ninomegadriver/TDBABootleg/ESP32_HW_Fantastic/resources/menu_kong.png

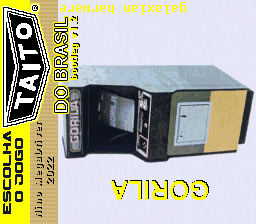
ESP32_HW_Fantastic/resources/menu_kong.png
