ninomegadriver/TDBABootleg/ESP32_HW_Invaders/resources/bkp/menu_indian.png

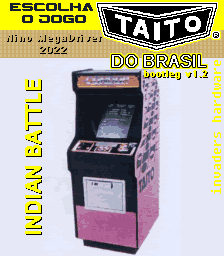
ESP32_HW_Invaders/resources/bkp/menu_indian.png
