ninomegadriver/TDBABootleg/ESP32_HW_Invaders/resources/bkp/menu_invaders.png

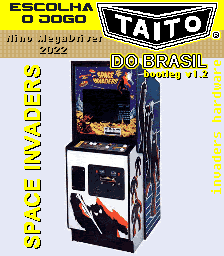
ESP32_HW_Invaders/resources/bkp/menu_invaders.png
