ninomegadriver/TDBABootleg/ESP32_HW_Invaders/resources/menu_galactica.png

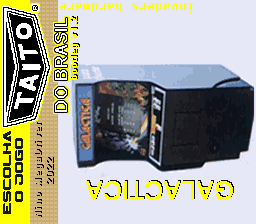
ESP32_HW_Invaders/resources/menu_galactica.png
