ninomegadriver/TDBABootleg/ESP32_HW_Invaders/resources/menu_indian.png

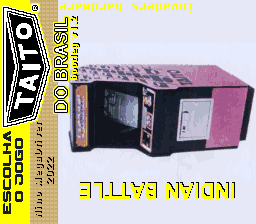
ESP32_HW_Invaders/resources/menu_indian.png
