ninomegadriver/TDBABootleg/ESP32_HW_Invaders/resources/menu_invaders.png

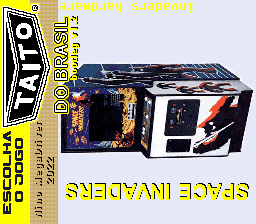
ESP32_HW_Invaders/resources/menu_invaders.png
