ninomegadriver/TDBABootleg/ESP32_HW_Fantastic/munch.hpp

#pragma GCC optimize ("O3")

// MAME: pacmanbl

void munch_pal(){
   pixel[0] = DisplayController.createRawPixel(RGB888(0,0,0));
   pixel[1] = DisplayController.createRawPixel(RGB888(0,0,0));
   pixel[2] = DisplayController.createRawPixel(RGB888(0,0,0));
   pixel[3] = DisplayController.createRawPixel(RGB888(195,195,217));
   pixel[4] = DisplayController.createRawPixel(RGB888(0,0,0));
   pixel[5] = DisplayController.createRawPixel(RGB888(195,62,0));
   pixel[6] = DisplayController.createRawPixel(RGB888(0,0,217));
   pixel[7] = DisplayController.createRawPixel(RGB888(224,224,0));
   pixel[8] = DisplayController.createRawPixel(RGB888(0,0,0));
   pixel[9] = DisplayController.createRawPixel(RGB888(0,91,217));
   pixel[10] = DisplayController.createRawPixel(RGB888(224,0,0));
   pixel[11] = DisplayController.createRawPixel(RGB888(224,224,0));
   pixel[12] = DisplayController.createRawPixel(RGB888(0,0,0));
   pixel[13] = DisplayController.createRawPixel(RGB888(0,0,217));
   pixel[14] = DisplayController.createRawPixel(RGB888(133,0,217));
   pixel[15] = DisplayController.createRawPixel(RGB888(224,0,0));
   pixel[16] = DisplayController.createRawPixel(RGB888(0,0,0));
   pixel[17] = DisplayController.createRawPixel(RGB888(0,0,217));
   pixel[18] = DisplayController.createRawPixel(RGB888(0,133,148));
   pixel[19] = DisplayController.createRawPixel(RGB888(133,29,0));
   pixel[20] = DisplayController.createRawPixel(RGB888(0,0,0));
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
1,1,0,0,0,0,0,1,1,0,0,0,0,0,0,0,0,0,0,0,0,0,0,0,0,0,0,0,0,0,0,0,0,
0,0,0,0,0,0,0,0,0,0,0,0,0,0,1,1,0,0,0,0,0,1,1,1,1,0,0,0,0,1,1,1,1,
0,0,0,0,0,1,1,0,0,0,0,0,0,0,0,0,0,0,0,0,0,0,0,0,0,0,0,0,1,1,1,1,0,
0,0,1,1,1,1,1,1,0,1,1,1,1,1,1,1,1,1,1,1,1,1,1,1,1,1,1,1,1,1,1,1,1,
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
