ninomegadriver/TDBABootleg/ESP32_HW_Invaders/galactic.hpp

#pragma GCC optimize ("O3")

#include "Arduino.h"

void galactic_layout(){
  for( int i=0; i<260; i++ ) {
    int   c = 2;                // verde
    if(i>=187 && i<=210) c = 3; // vermelho
    if(i>=60 && i<=186)  c = 4; // amarelo
    if(i>=45 && i<=59)   c = 5; // azul
    scanLineColor[i] = c;
  }
}

const uint8_t galactic[] = {
    0x00, 0x00, 0x00, 0xC3, 0x9B, 0x00, 0xFF, 0xFF, 0xC3, 0x40, 0x00, 0xFF, 0xFF, 0xFF, 0xFF, 0xFF, 0xC3, 0x40, 0x00, 0xFF, 
    0xFF, 0xFF, 0xFF, 0xFF, 0xC3, 0x40, 0x00, 0xFF, 0xFF, 0xFF, 0xFF, 0xFF, 0x77, 0x23, 0x05, 0xC2, 0x20, 0x00, 0xC9, 0xFF, 
    0x87, 0xE1, 0x5F, 0x16, 0x00, 0x19, 0x5E, 0x23, 0x56, 0xEB, 0xE9, 0xFF, 0xFF, 0xFF, 0xFF, 0xFF, 0x85, 0x6F, 0x3E, 0x00, 
    0x8C, 0x67, 0x7E, 0xC9, 0xF5, 0xC5, 0xD5, 0xE5, 0xD3, 0x06, 0x3A, 0x15, 0x20, 0x32, 0x16, 0x20, 0x3A, 0x13, 0x20, 0x32, 
    0x15, 0x20, 0x2A, 0x10, 0x20, 0x22, 0x13, 0x20, 0xDB, 0x00, 0x32, 0x12, 0x20, 0xDB, 0x02, 0x32, 0x11, 0x20, 0xDB, 0x01, 
    0x32, 0x10, 0x20, 0x21, 0x5F, 0x22, 0x35, 0xCD, 0x1F, 0x4E, 0xCD, 0x34, 0x4E, 0xCD, 0x35, 0x50, 0xCD, 0x96, 0x52, 0x3A, 
    0x3E, 0x20, 0xD3, 0x03, 0x3A, 0x3F, 0x20, 0xD3, 0x05, 0xCD, 0xD5, 0x1D, 0x21, 0x96, 0x00, 0xE5, 0x3A, 0x05, 0x20, 0xEF, 
    0xEB, 0x04, 0x2E, 0x05, 0x6B, 0x07, 0xAB, 0x08, 0x1F, 0x0B, 0xE1, 0xD1, 0xC1, 0xF1, 0xC9, 0x31, 0x00, 0x24, 0x3E, 0x00, 
    0xD3, 0x03, 0x32, 0x3E, 0x20, 0x3E, 0x0F, 0xD3, 0x05, 0x32, 0x3F, 0x20, 0x3E, 0xFF, 0xD3, 0x07, 0x21, 0x00, 0x20, 0xAF, 
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
    0x24, 0x1C, 0x1D, 0x0A, 0x1B, 0x1D, 0x24, 0x24, 0xFF, 0x0B, 0x2D, 0x13, 0x18, 0x10, 0x0A, 0x0D, 0x18, 0x1B, 0x24, 0x00, 
    0x01, 0xFF, 0x0B, 0x2D, 0x13, 0x18, 0x10, 0x0A, 0x0D, 0x18, 0x1B, 0x24, 0x00, 0x02, 0xFF, 0x1F, 0x2E, 0x1B, 0x0E, 0x0C, 
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
};
