ninomegadriver/TDBABootleg/ESP32_HW_Invaders/i8080.c

#pragma GCC optimize ("O3")


#include "i8080.h"

// this array defines the number of cycles one opcode takes.
// note that there are some special cases: conditional RETs and CALLs
// add +6 cycles if the condition is met
// clang-format off
static const uint8_t OPCODES_CYCLES[256] = {
//  0  1   2   3   4   5   6   7   8  9   A   B   C   D   E  F
    4, 10, 7,  5,  5,  5,  7,  4,  4, 10, 7,  5,  5,  5,  7, 4,  // 0
    4, 10, 7,  5,  5,  5,  7,  4,  4, 10, 7,  5,  5,  5,  7, 4,  // 1
    4, 10, 16, 5,  5,  5,  7,  4,  4, 10, 16, 5,  5,  5,  7, 4,  // 2
    4, 10, 13, 5,  10, 10, 10, 4,  4, 10, 13, 5,  5,  5,  7, 4,  // 3
    5, 5,  5,  5,  5,  5,  7,  5,  5, 5,  5,  5,  5,  5,  7, 5,  // 4
    5, 5,  5,  5,  5,  5,  7,  5,  5, 5,  5,  5,  5,  5,  7, 5,  // 5
    5, 5,  5,  5,  5,  5,  7,  5,  5, 5,  5,  5,  5,  5,  7, 5,  // 6
    7, 7,  7,  7,  7,  7,  7,  7,  5, 5,  5,  5,  5,  5,  7, 5,  // 7
    4, 4,  4,  4,  4,  4,  7,  4,  4, 4,  4,  4,  4,  4,  7, 4,  // 8
    4, 4,  4,  4,  4,  4,  7,  4,  4, 4,  4,  4,  4,  4,  7, 4,  // 9
    4, 4,  4,  4,  4,  4,  7,  4,  4, 4,  4,  4,  4,  4,  7, 4,  // A
    4, 4,  4,  4,  4,  4,  7,  4,  4, 4,  4,  4,  4,  4,  7, 4,  // B
    5, 10, 10, 10, 11, 11, 7,  11, 5, 10, 10, 10, 11, 17, 7, 11, // C
    5, 10, 10, 10, 11, 11, 7,  11, 5, 10, 10, 10, 11, 17, 7, 11, // D
    5, 10, 10, 18, 11, 11, 7,  11, 5, 5,  10, 4,  11, 17, 7, 11, // E
    5, 10, 10, 4,  11, 11, 7,  11, 5, 5,  10, 4,  11, 17, 7, 11  // F
};
// clang-format on

static const char* DISASSEMBLE_TABLE[] = {"nop", "lxi b,#", "stax b", "inx b",
    "inr b", "dcr b", "mvi b,#", "rlc", "ill", "dad b", "ldax b", "dcx b",
    "inr c", "dcr c", "mvi c,#", "rrc", "ill", "lxi d,#", "stax d", "inx d",
    "inr d", "dcr d", "mvi d,#", "ral", "ill", "dad d", "ldax d", "dcx d",
    "inr e", "dcr e", "mvi e,#", "rar", "ill", "lxi h,#", "shld", "inx h",
    "inr h", "dcr h", "mvi h,#", "daa", "ill", "dad h", "lhld", "dcx h",
    "inr l", "dcr l", "mvi l,#", "cma", "ill", "lxi sp,#", "sta $", "inx sp",
    "inr M", "dcr M", "mvi M,#", "stc", "ill", "dad sp", "lda $", "dcx sp",
    "inr a", "dcr a", "mvi a,#", "cmc", "mov b,b", "mov b,c", "mov b,d",
    "mov b,e", "mov b,h", "mov b,l", "mov b,M", "mov b,a", "mov c,b", "mov c,c",
    "mov c,d", "mov c,e", "mov c,h", "mov c,l", "mov c,M", "mov c,a", "mov d,b",
    "mov d,c", "mov d,d", "mov d,e", "mov d,h", "mov d,l", "mov d,M", "mov d,a",
    "mov e,b", "mov e,c", "mov e,d", "mov e,e", "mov e,h", "mov e,l", "mov e,M",
    "mov e,a", "mov h,b", "mov h,c", "mov h,d", "mov h,e", "mov h,h", "mov h,l",
    "mov h,M", "mov h,a", "mov l,b", "mov l,c", "mov l,d", "mov l,e", "mov l,h",
    "mov l,l", "mov l,M", "mov l,a", "mov M,b", "mov M,c", "mov M,d", "mov M,e",
    "mov M,h", "mov M,l", "hlt", "mov M,a", "mov a,b", "mov a,c", "mov a,d",
    "mov a,e", "mov a,h", "mov a,l", "mov a,M", "mov a,a", "add b", "add c",
    "add d", "add e", "add h", "add l", "add M", "add a", "adc b", "adc c",
    "adc d", "adc e", "adc h", "adc l", "adc M", "adc a", "sub b", "sub c",
    "sub d", "sub e", "sub h", "sub l", "sub M", "sub a", "sbb b", "sbb c",
    "sbb d", "sbb e", "sbb h", "sbb l", "sbb M", "sbb a", "ana b", "ana c",
    "ana d", "ana e", "ana h", "ana l", "ana M", "ana a", "xra b", "xra c",
    "xra d", "xra e", "xra h", "xra l", "xra M", "xra a", "ora b", "ora c",
    "ora d", "ora e", "ora h", "ora l", "ora M", "ora a", "cmp b", "cmp c",
    "cmp d", "cmp e", "cmp h", "cmp l", "cmp M", "cmp a", "rnz", "pop b",
    "jnz $", "jmp $", "cnz $", "push b", "adi #", "rst 0", "rz", "ret", "jz $",
    "ill", "cz $", "call $", "aci #", "rst 1", "rnc", "pop d", "jnc $", "out p",
    "cnc $", "push d", "sui #", "rst 2", "rc", "ill", "jc $", "in p", "cc $",
    "ill", "sbi #", "rst 3", "rpo", "pop h", "jpo $", "xthl", "cpo $", "push h",
    "ani #", "rst 4", "rpe", "pchl", "jpe $", "xchg", "cpe $", "ill", "xri #",
    "rst 5", "rp", "pop psw", "jp $", "di", "cp $", "push psw", "ori #",
    "rst 6", "rm", "sphl", "jm $", "ei", "cm $", "ill", "cpi #", "rst 7"};

#define SET_ZSP(c, val) \
  do { \
    c->zf = (val) == 0; \
    c->sf = (val) >> 7; \
    c->pf = parity(val); \
  } while (0)

// memory helpers (the only four to use `read_byte` and `write_byte` function
// pointers)

// reads a byte from memory
static inline uint8_t i8080_rb(i8080* const c, uint16_t addr) {
  return c->read_byte(c->userdata, addr);
}

// writes a byte to memory
static inline void i8080_wb(i8080* const c, uint16_t addr, uint8_t val) {
  c->write_byte(c->userdata, addr, val);
}

// reads a word from memory
static inline uint16_t i8080_rw(i8080* const c, uint16_t addr) {
  return c->read_byte(c->userdata, addr + 1) << 8 |
         c->read_byte(c->userdata, addr);
}

// writes a word to memory
static inline void i8080_ww(i8080* const c, uint16_t addr, uint16_t val) {
  c->write_byte(c->userdata, addr, val & 0xFF);
  c->write_byte(c->userdata, addr + 1, val >> 8);
}

// returns the next byte in memory (and updates the program counter)
static inline uint8_t i8080_next_byte(i8080* const c) {
  return i8080_rb(c, c->pc++);
}

// returns the next word in memory (and updates the program counter)
static inline uint16_t i8080_next_word(i8080* const c) {
  uint16_t result = i8080_rw(c, c->pc);
  c->pc += 2;
  return result;
}

// paired registers helpers (setters and getters)
static inline void i8080_set_bc(i8080* const c, uint16_t val) {
  c->b = val >> 8;
  c->c = val & 0xFF;
}

static inline void i8080_set_de(i8080* const c, uint16_t val) {
  c->d = val >> 8;
  c->e = val & 0xFF;
}

static inline void i8080_set_hl(i8080* const c, uint16_t val) {
  c->h = val >> 8;
  c->l = val & 0xFF;
}

static inline uint16_t i8080_get_bc(i8080* const c) {
  return (c->b << 8) | c->c;
}

static inline uint16_t i8080_get_de(i8080* const c) {
  return (c->d << 8) | c->e;
}

static inline uint16_t i8080_get_hl(i8080* const c) {
  return (c->h << 8) | c->l;
}

// stack helpers

// pushes a value into the stack and updates the stack pointer
static inline void i8080_push_stack(i8080* const c, uint16_t val) {
  c->sp -= 2;
  i8080_ww(c, c->sp, val);
}

// pops a value from the stack and updates the stack pointer
static inline uint16_t i8080_pop_stack(i8080* const c) {
  uint16_t val = i8080_rw(c, c->sp);
  c->sp += 2;
  return val;
}

// opcodes

// returns the parity of byte: 0 if number of 1 bits in `val` is odd, else 1
static inline bool parity(uint8_t val) {
  uint8_t nb_one_bits = 0;
  for (int i = 0; i < 8; i++) {
    nb_one_bits += ((val >> i) & 1);
  }

  return (nb_one_bits & 1) == 0;
}

// returns if there was a carry between bit "bit_no" and "bit_no - 1" when
// executing "a + b + cy"
static inline bool carry(int bit_no, uint8_t a, uint8_t b, bool cy) {
  int16_t result = a + b + cy;
  int16_t carry = result ^ a ^ b;
  return carry & (1 << bit_no);
}

// adds a value (+ an optional carry flag) to a register
static inline void i8080_add(
    i8080* const c, uint8_t* const reg, uint8_t val, bool cy) {
  uint8_t result = *reg + val + cy;
  c->cf = carry(8, *reg, val, cy);
  c->hf = carry(4, *reg, val, cy);
  SET_ZSP(c, result);
  *reg = result;
}

// substracts a byte (+ an optional carry flag) from a register
// see https://stackoverflow.com/a/8037485
static inline void i8080_sub(
    i8080* const c, uint8_t* const reg, uint8_t val, bool cy) {
  i8080_add(c, reg, ~val, !cy);
  c->cf = !c->cf;
}

// adds a word to HL
static inline void i8080_dad(i8080* const c, uint16_t val) {
  c->cf = ((i8080_get_hl(c) + val) >> 16) & 1;
  i8080_set_hl(c, i8080_get_hl(c) + val);
}

// increments a byte
static inline uint8_t i8080_inr(i8080* const c, uint8_t val) {
  uint8_t result = val + 1;
  c->hf = (result & 0xF) == 0;
  SET_ZSP(c, result);
  return result;
}

// decrements a byte
static inline uint8_t i8080_dcr(i8080* const c, uint8_t val) {
  uint8_t result = val - 1;
  c->hf = !((result & 0xF) == 0xF);
  SET_ZSP(c, result);
  return result;
}

// executes a logic "and" between register A and a byte, then stores the
// result in register A
static inline void i8080_ana(i8080* const c, uint8_t val) {
  uint8_t result = c->a & val;
  c->cf = 0;
  c->hf = ((c->a | val) & 0x08) != 0;
  SET_ZSP(c, result);
  c->a = result;
}

// executes a logic "xor" between register A and a byte, then stores the
// result in register A
static inline void i8080_xra(i8080* const c, uint8_t val) {
  c->a ^= val;
  c->cf = 0;
  c->hf = 0;
  SET_ZSP(c, c->a);
}

// executes a logic "or" between register A and a byte, then stores the
// result in register A
static inline void i8080_ora(i8080* const c, uint8_t val) {
  c->a |= val;
  c->cf = 0;
  c->hf = 0;
  SET_ZSP(c, c->a);
}

// compares the register A to another byte
static inline void i8080_cmp(i8080* const c, uint8_t val) {
  int16_t result = c->a - val;
  c->cf = result >> 8;
  c->hf = ~(c->a ^ result ^ val) & 0x10;
  SET_ZSP(c, result & 0xFF);
}

// sets the program counter to a given address
static inline void i8080_jmp(i8080* const c, uint16_t addr) {
  c->pc = addr;
}

// jumps to next address pointed by the next word in memory if a condition
// is met
static inline void i8080_cond_jmp(i8080* const c, bool condition) {
  uint16_t addr = i8080_next_word(c);
  if (condition) {
    c->pc = addr;
  }
}

// pushes the current pc to the stack, then jumps to an address
static inline void i8080_call(i8080* const c, uint16_t addr) {
  i8080_push_stack(c, c->pc);
  i8080_jmp(c, addr);
}

// calls to next word in memory if a condition is met
static inline void i8080_cond_call(i8080* const c, bool condition) {
  uint16_t addr = i8080_next_word(c);
  if (condition) {
    i8080_call(c, addr);
    c->cyc += 6;
  }
}

// returns from subroutine
static inline void i8080_ret(i8080* const c) {
  c->pc = i8080_pop_stack(c);
}

// returns from subroutine if a condition is met
static inline void i8080_cond_ret(i8080* const c, bool condition) {
  if (condition) {
    i8080_ret(c);
    c->cyc += 6;
  }
}

// pushes register A and the flags into the stack
static inline void i8080_push_psw(i8080* const c) {
  // note: bit 3 and 5 are always 0
  uint8_t psw = 0;
  psw |= c->sf << 7;
  psw |= c->zf << 6;
  psw |= c->hf << 4;
  psw |= c->pf << 2;
  psw |= 1 << 1; // bit 1 is always 1
  psw |= c->cf << 0;
  i8080_push_stack(c, c->a << 8 | psw);
}

// pops register A and the flags from the stack
static inline void i8080_pop_psw(i8080* const c) {
  uint16_t af = i8080_pop_stack(c);
  c->a = af >> 8;
  uint8_t psw = af & 0xFF;

  c->sf = (psw >> 7) & 1;
  c->zf = (psw >> 6) & 1;
  c->hf = (psw >> 4) & 1;
  c->pf = (psw >> 2) & 1;
  c->cf = (psw >> 0) & 1;
}

// rotate register A left
static inline void i8080_rlc(i8080* const c) {
  c->cf = c->a >> 7;
  c->a = (c->a << 1) | c->cf;
}

// rotate register A right
static inline void i8080_rrc(i8080* const c) {
  c->cf = c->a & 1;
  c->a = (c->a >> 1) | (c->cf << 7);
}

// rotate register A left with the carry flag
static inline void i8080_ral(i8080* const c) {
  bool cy = c->cf;
  c->cf = c->a >> 7;
  c->a = (c->a << 1) | cy;
}

// rotate register A right with the carry flag
static inline void i8080_rar(i8080* const c) {
  bool cy = c->cf;
  c->cf = c->a & 1;
  c->a = (c->a >> 1) | (cy << 7);
}

// Decimal Adjust Accumulator: the eight-bit number in register A is adjusted
// to form two four-bit binary-coded-decimal digits.
// For example, if A=$2B and DAA is executed, A becomes $31.
static inline void i8080_daa(i8080* const c) {
  bool cy = c->cf;
  uint8_t correction = 0;

  uint8_t lsb = c->a & 0x0F;
  uint8_t msb = c->a >> 4;

  if (c->hf || lsb > 9) {
    correction += 0x06;
  }

  if (c->cf || msb > 9 || (msb >= 9 && lsb > 9)) {
    correction += 0x60;
    cy = 1;
  }

  i8080_add(c, &c->a, correction, 0);
  c->cf = cy;
}

// switches the value of registers DE and HL
static inline void i8080_xchg(i8080* const c) {
  uint16_t de = i8080_get_de(c);
  i8080_set_de(c, i8080_get_hl(c));
  i8080_set_hl(c, de);
}

// switches the value of a word at (sp) and HL
static inline void i8080_xthl(i8080* const c) {
  uint16_t val = i8080_rw(c, c->sp);
  i8080_ww(c, c->sp, i8080_get_hl(c));
  i8080_set_hl(c, val);
}

// executes one opcode
static inline void i8080_execute(i8080* const c, uint8_t opcode) {
  c->cyc += OPCODES_CYCLES[opcode];

  // when DI is executed, interrupts won't be serviced
  // until the end of next instruction:
  if (c->interrupt_delay > 0) {
    c->interrupt_delay -= 1;
  }

  switch (opcode) {
  case 0x7F: c->a = c->a; break; // MOV A,A
  case 0x78: c->a = c->b; break; // MOV A,B
  case 0x79: c->a = c->c; break; // MOV A,C
  case 0x7A: c->a = c->d; break; // MOV A,D
  case 0x7B: c->a = c->e; break; // MOV A,E
  case 0x7C: c->a = c->h; break; // MOV A,H
  case 0x7D: c->a = c->l; break; // MOV A,L
  case 0x7E: c->a = i8080_rb(c, i8080_get_hl(c)); break; // MOV A,M

  case 0x0A: c->a = i8080_rb(c, i8080_get_bc(c)); break; // LDAX B
  case 0x1A: c->a = i8080_rb(c, i8080_get_de(c)); break; // LDAX D
  case 0x3A: c->a = i8080_rb(c, i8080_next_word(c)); break; // LDA word

  case 0x47: c->b = c->a; break; // MOV B,A
  case 0x40: c->b = c->b; break; // MOV B,B
  case 0x41: c->b = c->c; break; // MOV B,C
  case 0x42: c->b = c->d; break; // MOV B,D
  case 0x43: c->b = c->e; break; // MOV B,E
  case 0x44: c->b = c->h; break; // MOV B,H
  case 0x45: c->b = c->l; break; // MOV B,L
  case 0x46: c->b = i8080_rb(c, i8080_get_hl(c)); break; // MOV B,M

  case 0x4F: c->c = c->a; break; // MOV C,A
  case 0x48: c->c = c->b; break; // MOV C,B
  case 0x49: c->c = c->c; break; // MOV C,C
  case 0x4A: c->c = c->d; break; // MOV C,D
  case 0x4B: c->c = c->e; break; // MOV C,E
  case 0x4C: c->c = c->h; break; // MOV C,H
  case 0x4D: c->c = c->l; break; // MOV C,L
  case 0x4E: c->c = i8080_rb(c, i8080_get_hl(c)); break; // MOV C,M

  case 0x57: c->d = c->a; break; // MOV D,A
  case 0x50: c->d = c->b; break; // MOV D,B
  case 0x51: c->d = c->c; break; // MOV D,C
  case 0x52: c->d = c->d; break; // MOV D,D
  case 0x53: c->d = c->e; break; // MOV D,E
  case 0x54: c->d = c->h; break; // MOV D,H
  case 0x55: c->d = c->l; break; // MOV D,L
  case 0x56: c->d = i8080_rb(c, i8080_get_hl(c)); break; // MOV D,M

  case 0x5F: c->e = c->a; break; // MOV E,A
  case 0x58: c->e = c->b; break; // MOV E,B
  case 0x59: c->e = c->c; break; // MOV E,C
  case 0x5A: c->e = c->d; break; // MOV E,D
  case 0x5B: c->e = c->e; break; // MOV E,E
  case 0x5C: c->e = c->h; break; // MOV E,H
  case 0x5D: c->e = c->l; break; // MOV E,L
  case 0x5E: c->e = i8080_rb(c, i8080_get_hl(c)); break; // MOV E,M

  case 0x67: c->h = c->a; break; // MOV H,A
  case 0x60: c->h = c->b; break; // MOV H,B
  case 0x61: c->h = c->c; break; // MOV H,C
  case 0x62: c->h = c->d; break; // MOV H,D
  case 0x63: c->h = c->e; break; // MOV H,E
  case 0x64: c->h = c->h; break; // MOV H,H
  case 0x65: c->h = c->l; break; // MOV H,L
  case 0x66: c->h = i8080_rb(c, i8080_get_hl(c)); break; // MOV H,M

  case 0x6F: c->l = c->a; break; // MOV L,A
  case 0x68: c->l = c->b; break; // MOV L,B
  case 0x69: c->l = c->c; break; // MOV L,C
  case 0x6A: c->l = c->d; break; // MOV L,D
  case 0x6B: c->l = c->e; break; // MOV L,E
  case 0x6C: c->l = c->h; break; // MOV L,H
  case 0x6D: c->l = c->l; break; // MOV L,L
  case 0x6E: c->l = i8080_rb(c, i8080_get_hl(c)); break; // MOV L,M

  case 0x77: i8080_wb(c, i8080_get_hl(c), c->a); break; // MOV M,A
  case 0x70: i8080_wb(c, i8080_get_hl(c), c->b); break; // MOV M,B
  case 0x71: i8080_wb(c, i8080_get_hl(c), c->c); break; // MOV M,C
  case 0x72: i8080_wb(c, i8080_get_hl(c), c->d); break; // MOV M,D
  case 0x73: i8080_wb(c, i8080_get_hl(c), c->e); break; // MOV M,E
  case 0x74: i8080_wb(c, i8080_get_hl(c), c->h); break; // MOV M,H
  case 0x75: i8080_wb(c, i8080_get_hl(c), c->l); break; // MOV M,L

  case 0x3E: c->a = i8080_next_byte(c); break; // MVI A,byte
  case 0x06: c->b = i8080_next_byte(c); break; // MVI B,byte
  case 0x0E: c->c = i8080_next_byte(c); break; // MVI C,byte
  case 0x16: c->d = i8080_next_byte(c); break; // MVI D,byte
  case 0x1E: c->e = i8080_next_byte(c); break; // MVI E,byte
  case 0x26: c->h = i8080_next_byte(c); break; // MVI H,byte
  case 0x2E: c->l = i8080_next_byte(c); break; // MVI L,byte
  case 0x36:
    i8080_wb(c, i8080_get_hl(c), i8080_next_byte(c));
    break; // MVI M,byte

  case 0x02: i8080_wb(c, i8080_get_bc(c), c->a); break; // STAX B
  case 0x12: i8080_wb(c, i8080_get_de(c), c->a); break; // STAX D
  case 0x32: i8080_wb(c, i8080_next_word(c), c->a); break; // STA word

  case 0x01: i8080_set_bc(c, i8080_next_word(c)); break; // LXI B,word
  case 0x11: i8080_set_de(c, i8080_next_word(c)); break; // LXI D,word
  case 0x21: i8080_set_hl(c, i8080_next_word(c)); break; // LXI H,word
  case 0x31: c->sp = i8080_next_word(c); break; // LXI SP,word
  case 0x2A: i8080_set_hl(c, i8080_rw(c, i8080_next_word(c))); break; // LHLD
  case 0x22: i8080_ww(c, i8080_next_word(c), i8080_get_hl(c)); break; // SHLD
  case 0xF9: c->sp = i8080_get_hl(c); break; // SPHL

  case 0xEB: i8080_xchg(c); break; // XCHG
  case 0xE3: i8080_xthl(c); break; // XTHL

  case 0x87: i8080_add(c, &c->a, c->a, 0); break; // ADD A
  case 0x80: i8080_add(c, &c->a, c->b, 0); break; // ADD B
  case 0x81: i8080_add(c, &c->a, c->c, 0); break; // ADD C
  case 0x82: i8080_add(c, &c->a, c->d, 0); break; // ADD D
  case 0x83: i8080_add(c, &c->a, c->e, 0); break; // ADD E
  case 0x84: i8080_add(c, &c->a, c->h, 0); break; // ADD H
  case 0x85: i8080_add(c, &c->a, c->l, 0); break; // ADD L
  case 0x86:
    i8080_add(c, &c->a, i8080_rb(c, i8080_get_hl(c)), 0);
    break; // ADD M
  case 0xC6: i8080_add(c, &c->a, i8080_next_byte(c), 0); break; // ADI byte

  case 0x8F: i8080_add(c, &c->a, c->a, c->cf); break; // ADC A
  case 0x88: i8080_add(c, &c->a, c->b, c->cf); break; // ADC B
  case 0x89: i8080_add(c, &c->a, c->c, c->cf); break; // ADC C
  case 0x8A: i8080_add(c, &c->a, c->d, c->cf); break; // ADC D
  case 0x8B: i8080_add(c, &c->a, c->e, c->cf); break; // ADC E
  case 0x8C: i8080_add(c, &c->a, c->h, c->cf); break; // ADC H
  case 0x8D: i8080_add(c, &c->a, c->l, c->cf); break; // ADC L
  case 0x8E:
    i8080_add(c, &c->a, i8080_rb(c, i8080_get_hl(c)), c->cf);
    break; // ADC M
  case 0xCE: i8080_add(c, &c->a, i8080_next_byte(c), c->cf); break; // ACI byte

  case 0x97: i8080_sub(c, &c->a, c->a, 0); break; // SUB A
  case 0x90: i8080_sub(c, &c->a, c->b, 0); break; // SUB B
  case 0x91: i8080_sub(c, &c->a, c->c, 0); break; // SUB C
  case 0x92: i8080_sub(c, &c->a, c->d, 0); break; // SUB D
  case 0x93: i8080_sub(c, &c->a, c->e, 0); break; // SUB E
  case 0x94: i8080_sub(c, &c->a, c->h, 0); break; // SUB H
  case 0x95: i8080_sub(c, &c->a, c->l, 0); break; // SUB L
  case 0x96:
    i8080_sub(c, &c->a, i8080_rb(c, i8080_get_hl(c)), 0);
    break; // SUB M
  case 0xD6: i8080_sub(c, &c->a, i8080_next_byte(c), 0); break; // SUI byte

  case 0x9F: i8080_sub(c, &c->a, c->a, c->cf); break; // SBB A
  case 0x98: i8080_sub(c, &c->a, c->b, c->cf); break; // SBB B
  case 0x99: i8080_sub(c, &c->a, c->c, c->cf); break; // SBB C
  case 0x9A: i8080_sub(c, &c->a, c->d, c->cf); break; // SBB D
  case 0x9B: i8080_sub(c, &c->a, c->e, c->cf); break; // SBB E
  case 0x9C: i8080_sub(c, &c->a, c->h, c->cf); break; // SBB H
  case 0x9D: i8080_sub(c, &c->a, c->l, c->cf); break; // SBB L
  case 0x9E:
    i8080_sub(c, &c->a, i8080_rb(c, i8080_get_hl(c)), c->cf);
    break; // SBB M
  case 0xDE: i8080_sub(c, &c->a, i8080_next_byte(c), c->cf); break; // SBI byte

  case 0x09: i8080_dad(c, i8080_get_bc(c)); break; // DAD B
  case 0x19: i8080_dad(c, i8080_get_de(c)); break; // DAD D
  case 0x29: i8080_dad(c, i8080_get_hl(c)); break; // DAD H
  case 0x39: i8080_dad(c, c->sp); break; // DAD SP

  case 0xF3: c->iff = 0; break; // DI
  case 0xFB:
    c->iff = 1;
    c->interrupt_delay = 1;
    break; // EI
  case 0x00: break; // NOP
  case 0x76: c->halted = 1; break; // HLT

  case 0x3C: c->a = i8080_inr(c, c->a); break; // INR A
  case 0x04: c->b = i8080_inr(c, c->b); break; // INR B
  case 0x0C: c->c = i8080_inr(c, c->c); break; // INR C
  case 0x14: c->d = i8080_inr(c, c->d); break; // INR D
  case 0x1C: c->e = i8080_inr(c, c->e); break; // INR E
  case 0x24: c->h = i8080_inr(c, c->h); break; // INR H
  case 0x2C: c->l = i8080_inr(c, c->l); break; // INR L
  case 0x34:
    i8080_wb(c, i8080_get_hl(c), i8080_inr(c, i8080_rb(c, i8080_get_hl(c))));
    break; // INR M

  case 0x3D: c->a = i8080_dcr(c, c->a); break; // DCR A
  case 0x05: c->b = i8080_dcr(c, c->b); break; // DCR B
  case 0x0D: c->c = i8080_dcr(c, c->c); break; // DCR C
  case 0x15: c->d = i8080_dcr(c, c->d); break; // DCR D
  case 0x1D: c->e = i8080_dcr(c, c->e); break; // DCR E
  case 0x25: c->h = i8080_dcr(c, c->h); break; // DCR H
  case 0x2D: c->l = i8080_dcr(c, c->l); break; // DCR L
  case 0x35:
    i8080_wb(c, i8080_get_hl(c), i8080_dcr(c, i8080_rb(c, i8080_get_hl(c))));
    break; // DCR M

  case 0x03: i8080_set_bc(c, i8080_get_bc(c) + 1); break; // INX B
  case 0x13: i8080_set_de(c, i8080_get_de(c) + 1); break; // INX D
  case 0x23: i8080_set_hl(c, i8080_get_hl(c) + 1); break; // INX H
  case 0x33: c->sp += 1; break; // INX SP

  case 0x0B: i8080_set_bc(c, i8080_get_bc(c) - 1); break; // DCX B
  case 0x1B: i8080_set_de(c, i8080_get_de(c) - 1); break; // DCX D
  case 0x2B: i8080_set_hl(c, i8080_get_hl(c) - 1); break; // DCX H
  case 0x3B: c->sp -= 1; break; // DCX SP

  case 0x27: i8080_daa(c); break; // DAA
  case 0x2F: c->a = ~c->a; break; // CMA
  case 0x37: c->cf = 1; break; // STC
  case 0x3F: c->cf = !c->cf; break; // CMC

  case 0x07: i8080_rlc(c); break; // RLC (rotate left)
  case 0x0F: i8080_rrc(c); break; // RRC (rotate right)
  case 0x17: i8080_ral(c); break; // RAL
  case 0x1F: i8080_rar(c); break; // RAR

  case 0xA7: i8080_ana(c, c->a); break; // ANA A
  case 0xA0: i8080_ana(c, c->b); break; // ANA B
  case 0xA1: i8080_ana(c, c->c); break; // ANA C
  case 0xA2: i8080_ana(c, c->d); break; // ANA D
  case 0xA3: i8080_ana(c, c->e); break; // ANA E
  case 0xA4: i8080_ana(c, c->h); break; // ANA H
  case 0xA5: i8080_ana(c, c->l); break; // ANA L
  case 0xA6: i8080_ana(c, i8080_rb(c, i8080_get_hl(c))); break; // ANA M
  case 0xE6: i8080_ana(c, i8080_next_byte(c)); break; // ANI byte

  case 0xAF: i8080_xra(c, c->a); break; // XRA A
  case 0xA8: i8080_xra(c, c->b); break; // XRA B
  case 0xA9: i8080_xra(c, c->c); break; // XRA C
  case 0xAA: i8080_xra(c, c->d); break; // XRA D
  case 0xAB: i8080_xra(c, c->e); break; // XRA E
  case 0xAC: i8080_xra(c, c->h); break; // XRA H
  case 0xAD: i8080_xra(c, c->l); break; // XRA L
  case 0xAE: i8080_xra(c, i8080_rb(c, i8080_get_hl(c))); break; // XRA M
  case 0xEE: i8080_xra(c, i8080_next_byte(c)); break; // XRI byte

  case 0xB7: i8080_ora(c, c->a); break; // ORA A
  case 0xB0: i8080_ora(c, c->b); break; // ORA B
  case 0xB1: i8080_ora(c, c->c); break; // ORA C
  case 0xB2: i8080_ora(c, c->d); break; // ORA D
  case 0xB3: i8080_ora(c, c->e); break; // ORA E
  case 0xB4: i8080_ora(c, c->h); break; // ORA H
  case 0xB5: i8080_ora(c, c->l); break; // ORA L
  case 0xB6: i8080_ora(c, i8080_rb(c, i8080_get_hl(c))); break; // ORA M
  case 0xF6: i8080_ora(c, i8080_next_byte(c)); break; // ORI byte

  case 0xBF: i8080_cmp(c, c->a); break; // CMP A
  case 0xB8: i8080_cmp(c, c->b); break; // CMP B
  case 0xB9: i8080_cmp(c, c->c); break; // CMP C
  case 0xBA: i8080_cmp(c, c->d); break; // CMP D
  case 0xBB: i8080_cmp(c, c->e); break; // CMP E
  case 0xBC: i8080_cmp(c, c->h); break; // CMP H
  case 0xBD: i8080_cmp(c, c->l); break; // CMP L
  case 0xBE: i8080_cmp(c, i8080_rb(c, i8080_get_hl(c))); break; // CMP M
  case 0xFE: i8080_cmp(c, i8080_next_byte(c)); break; // CPI byte

  case 0xC3: i8080_jmp(c, i8080_next_word(c)); break; // JMP
  case 0xC2: i8080_cond_jmp(c, c->zf == 0); break; // JNZ
  case 0xCA: i8080_cond_jmp(c, c->zf == 1); break; // JZ
  case 0xD2: i8080_cond_jmp(c, c->cf == 0); break; // JNC
  case 0xDA: i8080_cond_jmp(c, c->cf == 1); break; // JC
  case 0xE2: i8080_cond_jmp(c, c->pf == 0); break; // JPO
  case 0xEA: i8080_cond_jmp(c, c->pf == 1); break; // JPE
  case 0xF2: i8080_cond_jmp(c, c->sf == 0); break; // JP
  case 0xFA: i8080_cond_jmp(c, c->sf == 1); break; // JM

  case 0xE9: c->pc = i8080_get_hl(c); break; // PCHL
  case 0xCD: i8080_call(c, i8080_next_word(c)); break; // CALL

  case 0xC4: i8080_cond_call(c, c->zf == 0); break; // CNZ
  case 0xCC: i8080_cond_call(c, c->zf == 1); break; // CZ
  case 0xD4: i8080_cond_call(c, c->cf == 0); break; // CNC
  case 0xDC: i8080_cond_call(c, c->cf == 1); break; // CC
  case 0xE4: i8080_cond_call(c, c->pf == 0); break; // CPO
  case 0xEC: i8080_cond_call(c, c->pf == 1); break; // CPE
  case 0xF4: i8080_cond_call(c, c->sf == 0); break; // CP
  case 0xFC: i8080_cond_call(c, c->sf == 1); break; // CM

  case 0xC9: i8080_ret(c); break; // RET
  case 0xC0: i8080_cond_ret(c, c->zf == 0); break; // RNZ
  case 0xC8: i8080_cond_ret(c, c->zf == 1); break; // RZ
  case 0xD0: i8080_cond_ret(c, c->cf == 0); break; // RNC
  case 0xD8: i8080_cond_ret(c, c->cf == 1); break; // RC
  case 0xE0: i8080_cond_ret(c, c->pf == 0); break; // RPO
  case 0xE8: i8080_cond_ret(c, c->pf == 1); break; // RPE
  case 0xF0: i8080_cond_ret(c, c->sf == 0); break; // RP
  case 0xF8: i8080_cond_ret(c, c->sf == 1); break; // RM

  case 0xC7: i8080_call(c, 0x00); break; // RST 0
  case 0xCF: i8080_call(c, 0x08); break; // RST 1
  case 0xD7: i8080_call(c, 0x10); break; // RST 2
  case 0xDF: i8080_call(c, 0x18); break; // RST 3
  case 0xE7: i8080_call(c, 0x20); break; // RST 4
  case 0xEF: i8080_call(c, 0x28); break; // RST 5
  case 0xF7: i8080_call(c, 0x30); break; // RST 6
  case 0xFF: i8080_call(c, 0x38); break; // RST 7

  case 0xC5: i8080_push_stack(c, i8080_get_bc(c)); break; // PUSH B
  case 0xD5: i8080_push_stack(c, i8080_get_de(c)); break; // PUSH D
  case 0xE5: i8080_push_stack(c, i8080_get_hl(c)); break; // PUSH H
  case 0xF5: i8080_push_psw(c); break; // PUSH PSW
  case 0xC1: i8080_set_bc(c, i8080_pop_stack(c)); break; // POP B
  case 0xD1: i8080_set_de(c, i8080_pop_stack(c)); break; // POP D
  case 0xE1: i8080_set_hl(c, i8080_pop_stack(c)); break; // POP H
  case 0xF1: i8080_pop_psw(c); break; // POP PSW

  case 0xDB: c->a = c->port_in(c->userdata, i8080_next_byte(c)); break; // IN
  case 0xD3: c->port_out(c->userdata, i8080_next_byte(c), c->a); break; // OUT

  case 0x08:
  case 0x10:
  case 0x18:
  case 0x20:
  case 0x28:
  case 0x30:
  case 0x38: break; // undocumented NOPs

  case 0xD9: i8080_ret(c); break; // undocumented RET

  case 0xDD:
  case 0xED:
  case 0xFD: i8080_call(c, i8080_next_word(c)); break; // undocumented CALLs

  case 0xCB: i8080_jmp(c, i8080_next_word(c)); break; // undocumented JMP
  }
}

// initialises the emulator with default values
void i8080_init(i8080* const c) {
  c->read_byte = NULL;
  c->write_byte = NULL;
  c->port_in = NULL;
  c->port_out = NULL;
  c->userdata = NULL;

  c->cyc = 0;

  c->pc = 0;
  c->sp = 0;

  c->a = 0;
  c->b = 0;
  c->c = 0;
  c->d = 0;
  c->e = 0;
  c->h = 0;
  c->l = 0;

  c->sf = 0;
  c->zf = 0;
  c->hf = 0;
  c->pf = 0;
  c->cf = 0;
  c->iff = 0;

  c->halted = 0;
  c->interrupt_pending = 0;
  c->interrupt_vector = 0;
  c->interrupt_delay = 0;
}

// executes one instruction
void i8080_step(i8080* const c) {
  // interrupt processing: if an interrupt is pending and IFF is set,
  // we execute the interrupt vector passed by the user.
  if (c->interrupt_pending && c->iff && c->interrupt_delay == 0) {
    c->interrupt_pending = 0;
    c->iff = 0;
    c->halted = 0;
    i8080_execute(c, c->interrupt_vector);
  } else if (!c->halted) {
    i8080_execute(c, i8080_next_byte(c));
  } else if (c->halted){
    c->halted = 0;
    c->pc++;
  }
}

// asks for an interrupt to be serviced
void i8080_interrupt(i8080* const c, uint8_t opcode) {
  c->interrupt_pending = 1;
  c->interrupt_vector = opcode;
}

void invaders_irq(i8080* const c, unsigned address )
{
  uint8_t vector;
  if(address == 0x10) vector = 207;
  if(address == 0x08) vector = 215;
  c->interrupt_pending = 0;
  i8080_execute(c, vector);
}

#undef SET_ZSP
