ninomegadriver/TDBABootleg/ESP32_HW_Invaders/indianbtbr.hpp

#pragma GCC optimize ("O3")

void indianbtbr_layout(){
  for( int i=0; i<260; i++ ) {
    int   c = 1;
    if( i <= 80 ) c = 2;
    else c = 1;
    scanLineColor[i] = c;
  }  
}

const uint8_t indianbtbr[] = {
    0x00, 0x00, 0x00, 0xDB, 0x00, 0xC3, 0xE7, 0x5D, 0xFB, 0xC9, 0x71, 0xC3, 0x5E, 0x54, 0x01, 0x44, 0xF5, 0xC5, 0xD5, 0xE5, 
    0xC3, 0x40, 0x00, 0x00, 0xC3, 0xA8, 0x0F, 0x21, 0x2E, 0x73, 0x71, 0x23, 0x3A, 0x03, 0x23, 0x67, 0xC9, 0x2C, 0x46, 0x21, 
    0xC3, 0xB3, 0x02, 0x23, 0x70, 0x21, 0xEA, 0x70, 0xC3, 0xAC, 0x04, 0x21, 0x32, 0x73, 0x71, 0x23, 0xC3, 0xF0, 0x04, 0x70, 
    0x59, 0x50, 0x0E, 0x00, 0x21, 0x00, 0x23, 0x35, 0x23, 0x34, 0x00, 0x00, 0x00, 0xDB, 0x01, 0x0F, 0xDA, 0x8D, 0x00, 0x3A, 
    0x09, 0x23, 0xA7, 0xCA, 0x6B, 0x00, 0x3A, 0x0A, 0x23, 0xFE, 0x06, 0xD2, 0x67, 0x00, 0xC6, 0x01, 0x27, 0x32, 0x0A, 0x23, 
    0xCD, 0x68, 0x04, 0xAF, 0x32, 0x09, 0x23, 0x3A, 0x08, 0x23, 0xA7, 0xCA, 0x87, 0x00, 0x3A, 0x0D, 0x23, 0xA7, 0xC2, 0xDB, 
    0x06, 0x3A, 0x0A, 0x23, 0xA7, 0xC2, 0x92, 0x00, 0x3A, 0x0B, 0x23, 0xA7, 0xC2, 0xDB, 0x06, 0xE1, 0xD1, 0xC1, 0xF1, 0xFB, 
    0xC9, 0x3E, 0x01, 0xC3, 0x68, 0x00, 0x3A, 0x18, 0x20, 0xA7, 0xC2, 0x87, 0x00, 0x3E, 0x01, 0x32, 0x18, 0x20, 0xAF, 0x32, 
    0x0B, 0x23, 0x31, 0xFF, 0x23, 0xFB, 0xCD, 0xB7, 0x01, 0xCD, 0x79, 0x04, 0x21, 0x16, 0x30, 0x11, 0xA1, 0x44, 0x0E, 0x04, 
    0xCD, 0xC1, 0x02, 0xD3, 0x06, 0x3A, 0x0A, 0x23, 0x3D, 0xD3, 0x06, 0x21, 0x12, 0x28, 0x0E, 0x14, 0xC2, 0x97, 0x01, 0x11, 
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
    0x27, 0x77, 0x5F, 0x23, 0x7E, 0x8A, 0x27, 0x77, 0x57, 0x23, 0x7E, 0x23, 0x66, 0x6F, 0x7A, 0xCD, 0x0B, 0x03, 0x7B, 0xD5, 
    0xF5, 0x0F, 0x0F, 0x0F, 0x0F, 0xE6, 0x0F, 0xCD, 0x1E, 0x03, 0xF1, 0xE6, 0x0F, 0xCD, 0x1E, 0x03, 0xD1, 0xC9, 0xC6, 0x1C, 
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
};
