ninomegadriver/TDBABootleg/ESP32_HW_Invaders/invaders.hpp

#pragma GCC optimize ("O3")

void invaders_layout(){
  for( int i=0; i<260; i++ ) {
    int   c = 1;
    if( i < 80 ) c = 2;
    else c = 1;
    scanLineColor[i] = c;
  }  
}

const uint8_t invaders[] = {
    0x00, 0x00, 0x00, 0xC3, 0xD4, 0x18, 0x00, 0x00, 0xF5, 0xC5, 0xD5, 0xE5, 0xC3, 0x8C, 0x00, 0x00, 0xF5, 0xC5, 0xD5, 0xE5, 
    0x3E, 0x80, 0x32, 0x72, 0x20, 0x21, 0xC0, 0x20, 0x35, 0xCD, 0xCD, 0x17, 0xDB, 0x01, 0x0F, 0xDA, 0x67, 0x00, 0x3A, 0xEA, 
    0x20, 0xA7, 0xCA, 0x42, 0x00, 0x3A, 0xEB, 0x20, 0xFE, 0x99, 0xCA, 0x3E, 0x00, 0xC6, 0x01, 0x27, 0x32, 0xEB, 0x20, 0xCD, 
    0x47, 0x19, 0xAF, 0x32, 0xEA, 0x20, 0x3A, 0xE9, 0x20, 0xA7, 0xCA, 0x82, 0x00, 0x3A, 0xEF, 0x20, 0xA7, 0xC2, 0x6F, 0x00, 
    0x3A, 0xEB, 0x20, 0xA7, 0xC2, 0x5D, 0x00, 0xCD, 0xBF, 0x0A, 0xC3, 0x82, 0x00, 0x3A, 0x93, 0x20, 0xA7, 0xC2, 0x82, 0x00, 
    0xC3, 0x65, 0x07, 0x3E, 0x01, 0x32, 0xEA, 0x20, 0xC3, 0x3F, 0x00, 0xCD, 0x40, 0x17, 0x3A, 0x32, 0x20, 0x32, 0x80, 0x20, 
    0xCD, 0x00, 0x01, 0xCD, 0x48, 0x02, 0xCD, 0x13, 0x09, 0x00, 0xE1, 0xD1, 0xC1, 0xF1, 0xFB, 0xC9, 0x00, 0x00, 0x00, 0x00, 
    0xAF, 0x32, 0x72, 0x20, 0x3A, 0xE9, 0x20, 0xA7, 0xCA, 0x82, 0x00, 0x3A, 0xEF, 0x20, 0xA7, 0xC2, 0xA5, 0x00, 0x3A, 0xC1, 
    0x20, 0x0F, 0xD2, 0x82, 0x00, 0x21, 0x20, 0x20, 0xCD, 0x4B, 0x02, 0xCD, 0x41, 0x01, 0xC3, 0x82, 0x00, 0xCD, 0x86, 0x08, 
    0xE5, 0x7E, 0x23, 0x66, 0x6F, 0x22, 0x09, 0x20, 0x22, 0x0B, 0x20, 0xE1, 0x2B, 0x7E, 0xFE, 0x03, 0xC2, 0xC8, 0x00, 0x3D, 
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
    0xCD, 0x78, 0x08, 0x73, 0x23, 0x72, 0x2B, 0x2B, 0x70, 0x00, 0xCD, 0xE4, 0x01, 0xF1, 0x0F, 0x3E, 0x21, 0x06, 0x00, 0xD2, 
    0x12, 0x03, 0x06, 0x20, 0x3E, 0x22, 0x32, 0x67, 0x20, 0xCD, 0xB6, 0x0A, 0xAF, 0x32, 0x11, 0x20, 0x78, 0xD3, 0x05, 0x3C, 
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
};
int invaders_length=65535;
