ninomegadriver/TDBABootleg/ESP32_HW_Invaders/invadpt2br.hpp

#pragma GCC optimize ("O3")

void invadpt2br_layout(){
  for( int i=0; i<260; i++ ) {
    int   c = 1;
    if( i <= 80 ) c = 2;
    else c = 1;
    scanLineColor[i] = c;
  }  
}

const uint8_t invadpt2br[] = {
    0x00, 0x00, 0x00, 0xC3, 0x8F, 0x16, 0x00, 0x00, 0xF5, 0xC5, 0xD5, 0xE5, 0xC3, 0x83, 0x0D, 0x00, 0xF5, 0xC5, 0xD5, 0xE5, 
    0x3E, 0x80, 0x32, 0x72, 0x20, 0x21, 0xC0, 0x20, 0x35, 0xCD, 0xF5, 0x15, 0xDB, 0x01, 0x0F, 0xDA, 0x70, 0x00, 0x3A, 0xEA, 
    0x20, 0xA7, 0xCA, 0x4B, 0x00, 0x3A, 0xEB, 0x20, 0xFE, 0x09, 0xCA, 0x47, 0x00, 0xC6, 0x01, 0x27, 0x32, 0xEB, 0x20, 0x3A, 
    0xCC, 0x20, 0xC6, 0x01, 0x27, 0x32, 0xCC, 0x20, 0xCD, 0x05, 0x17, 0xAF, 0x32, 0xEA, 0x20, 0x3A, 0xE9, 0x20, 0xA7, 0xCA, 
    0x8A, 0x00, 0x3A, 0xEF, 0x20, 0xA7, 0xC2, 0x75, 0x00, 0x3A, 0xEB, 0x20, 0xA7, 0xC2, 0x66, 0x00, 0xCD, 0xAE, 0x0C, 0xC3, 
    0x8A, 0x00, 0x3A, 0x93, 0x20, 0xA7, 0xC2, 0x94, 0x00, 0xC3, 0x45, 0x08, 0x3E, 0x01, 0xC3, 0x48, 0x00, 0xCD, 0x69, 0x15, 
    0xCD, 0x83, 0x43, 0x3A, 0x32, 0x20, 0x32, 0x80, 0x20, 0xCD, 0x0F, 0x01, 0xCD, 0x8E, 0x02, 0xCD, 0xFC, 0x0A, 0x3A, 0xB9, 
    0x20, 0xA7, 0xC4, 0x69, 0x15, 0xCD, 0x2D, 0x19, 0x21, 0xEB, 0x20, 0x7E, 0x2E, 0xCC, 0xBE, 0xC2, 0x03, 0x00, 0xE1, 0xD1, 
    0xC1, 0xF1, 0xFB, 0xC9, 0xAF, 0x32, 0x72, 0x20, 0x3A, 0xE9, 0x20, 0xA7, 0xCA, 0x8A, 0x00, 0x3A, 0xEF, 0x20, 0xA7, 0xC2, 
    0xBD, 0x00, 0x3A, 0xC1, 0x20, 0x0F, 0xD2, 0x94, 0x00, 0xCD, 0xEC, 0x42, 0x21, 0x20, 0x20, 0xCD, 0x91, 0x02, 0xCD, 0x5F, 
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
    0x10, 0xCD, 0xB9, 0x11, 0xCD, 0x10, 0x12, 0x21, 0x10, 0x20, 0x11, 0x10, 0x1B, 0x06, 0x10, 0xCD, 0xB2, 0x17, 0x06, 0x00, 
    0xCD, 0x5C, 0x17, 0x3A, 0x6D, 0x20, 0xA7, 0xC0, 0x3A, 0xEF, 0x20, 0xA7, 0xC8, 0x31, 0x00, 0x24, 0xFB, 0xCD, 0x58, 0x17, 
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
};
int invadpt2br_length=65535;
