ninomegadriver/TDBABootleg/ESP32_HW_Invaders/polarisbr.hpp

#pragma GCC optimize ("O3")

void polarisbr_layout(){
  for( int i=0; i<260; i++ ) {
    int   c = 1;
    if( i <= 80 ) c = 2;
    else c = 1;
    scanLineColor[i] = c;
  }  
}

const uint8_t polarisbr[] = {
    0x00, 0x00, 0x00, 0xC3, 0xC6, 0x05, 0x00, 0x00, 0xF5, 0xC5, 0xD5, 0xE5, 0xC3, 0xA7, 0x51, 0x00, 0xF5, 0xC5, 0xD5, 0xE5, 
    0xC3, 0x40, 0x00, 0x00, 0xC3, 0x6E, 0x0A, 0xE5, 0xFF, 0x11, 0x05, 0x09, 0x3A, 0x03, 0x23, 0x67, 0xC9, 0x0C, 0x49, 0x01, 
    0xC3, 0xD8, 0x02, 0xAB, 0x07, 0x21, 0xF0, 0x20, 0xC3, 0xD6, 0x04, 0x2A, 0x21, 0x20, 0x01, 0x04, 0xC3, 0x2F, 0x0B, 0x06, 
    0x57, 0x00, 0x00, 0x43, 0x21, 0x00, 0x23, 0x35, 0x23, 0x34, 0xCD, 0x1B, 0x04, 0xDB, 0x01, 0x0F, 0xDA, 0x90, 0x00, 0x3A, 
    0x09, 0x23, 0xA7, 0xCA, 0x6B, 0x00, 0x3A, 0x0A, 0x23, 0xFE, 0x18, 0xD2, 0x67, 0x00, 0xC6, 0x01, 0x27, 0x32, 0x0A, 0x23, 
    0xCD, 0x8F, 0x04, 0xAF, 0x32, 0x09, 0x23, 0x3A, 0x08, 0x23, 0xA7, 0xCA, 0x87, 0x00, 0x3A, 0x0D, 0x23, 0xA7, 0xC2, 0x64, 
    0x09, 0x3A, 0x0A, 0x23, 0xA7, 0xC2, 0x95, 0x00, 0x3A, 0x0B, 0x23, 0xA7, 0xC2, 0x64, 0x09, 0xCD, 0xA9, 0x16, 0xE1, 0xD1, 
    0xC1, 0xF1, 0xFB, 0xC9, 0x3E, 0x01, 0xC3, 0x68, 0x00, 0x3A, 0x4C, 0x20, 0xA7, 0xC2, 0x87, 0x00, 0x3E, 0x01, 0x32, 0x4C, 
    0x20, 0xAF, 0x32, 0x0B, 0x23, 0x31, 0xFF, 0x23, 0xFB, 0xCD, 0xD9, 0x01, 0xCD, 0xA0, 0x04, 0x21, 0x16, 0x30, 0x11, 0x79, 
    0x42, 0x0E, 0x04, 0xCD, 0xE6, 0x02, 0xD3, 0x05, 0x3A, 0x0A, 0x23, 0x3D, 0xD3, 0x05, 0x21, 0x12, 0x28, 0x0E, 0x14, 0xC2, 
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
    0x05, 0xCD, 0xDB, 0x03, 0xC5, 0xAF, 0x77, 0x01, 0x20, 0x00, 0x09, 0x77, 0x09, 0x77, 0x09, 0xC1, 0xC9, 0xCD, 0x48, 0x03, 
    0x3A, 0x11, 0x23, 0xA7, 0xC8, 0xAF, 0x32, 0x11, 0x23, 0xE5, 0x2A, 0x12, 0x23, 0xEB, 0xE1, 0x7E, 0x83, 0x27, 0x77, 0x5F, 
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
};
int polarisbr_length=65535;
