ninomegadriver/TDBABootleg/ESP32_HW_Fantastic/gorila_title.hpp

#pragma GCC optimize ("O3")
/*
 * "GORILA" (a.k.a. "kong") logo screen modifications
 */

/*  Called to replace the logo screen
 *  as seen on historical flyers and advertisers
 *  by Taito do Brasil
 */
void gorila_title(){

      int x = 16;
      int y = 80;

      // "GORILA" graphics using the default tile
      drawtilenew(16,x+8,y+0,1,0,0,2);
      drawtilenew(176,x+16,y+0,1,0,0,2);
      drawtilenew(176,x+24,y+0,1,0,0,2);
      drawtilenew(176,x+32,y+0,1,0,0,2);
      drawtilenew(176,x+40,y+0,1,0,0,2);
      drawtilenew(16,x+48,y+0,1,0,0,2);
      drawtilenew(176,x+56,y+0,1,0,0,2);
      drawtilenew(176,x+64,y+0,1,0,0,2);
      drawtilenew(176,x+72,y+0,1,0,0,2);
      drawtilenew(176,x+80,y+0,1,0,0,2);
      drawtilenew(16,x+88,y+0,1,0,0,2);
      drawtilenew(176,x+96,y+0,1,0,0,2);
      drawtilenew(176,x+104,y+0,1,0,0,2);
      drawtilenew(176,x+112,y+0,1,0,0,2);
      drawtilenew(176,x+120,y+0,1,0,0,2);
      drawtilenew(16,x+128,y+0,1,0,0,2);
      drawtilenew(176,x+136,y+0,1,0,0,2);
      drawtilenew(16,x+144,y+0,1,0,0,2);
      drawtilenew(176,x+152,y+0,1,0,0,2);
      drawtilenew(16,x+160,y+0,1,0,0,2);
      drawtilenew(16,x+168,y+0,1,0,0,2);
      drawtilenew(16,x+176,y+0,1,0,0,2);
      drawtilenew(16,x+184,y+0,1,0,0,2);
      drawtilenew(176,x+192,y+0,1,0,0,2);
      drawtilenew(176,x+200,y+0,1,0,0,2);
      drawtilenew(176,x+208,y+0,1,0,0,2);
      drawtilenew(176,x+216,y+0,1,0,0,2);
      drawtilenew(16,x+224,y+0,1,0,0,2);
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
      drawtilenew(16,x+200,y+96,color,0,0,2);
      drawtilenew(16,x+208,y+96,color,0,0,2);
      drawtilenew(16,x+216,y+96,color,0,0,2);
      drawtilenew(16,x+224,y+96,color,0,0,2);
      drawtilenew(16,x+232,y+96,color,0,0,2);
      drawtilenew(16,x+240,y+96,color,0,0,2);
}
