ninomegadriver/TDBABootleg/ESP32_HW_Fantastic/kong.hpp

#pragma GCC optimize ("O3")

/*
 * "GORILA" (a.k.a. "kong") game ROM, palette and decoded graphics
 */

// Decoded color pallete
void kong_pal(){
   pixel[0] = DisplayController.createRawPixel(RGB888(0,0,0));
   pixel[1] = DisplayController.createRawPixel(RGB888(195,224,148));
   pixel[2] = DisplayController.createRawPixel(RGB888(62,91,217));
   pixel[3] = DisplayController.createRawPixel(RGB888(133,91,69));
   pixel[4] = DisplayController.createRawPixel(RGB888(0,0,0));
   pixel[5] = DisplayController.createRawPixel(RGB888(162,91,0));
   pixel[6] = DisplayController.createRawPixel(RGB888(0,162,217));
   pixel[7] = DisplayController.createRawPixel(RGB888(62,62,148));
   pixel[8] = DisplayController.createRawPixel(RGB888(0,0,0));
   pixel[9] = DisplayController.createRawPixel(RGB888(162,91,0));
   pixel[10] = DisplayController.createRawPixel(RGB888(91,162,69));
   pixel[11] = DisplayController.createRawPixel(RGB888(195,91,0));
   pixel[12] = DisplayController.createRawPixel(RGB888(0,0,0));
   pixel[13] = DisplayController.createRawPixel(RGB888(29,0,69));
   pixel[14] = DisplayController.createRawPixel(RGB888(162,0,217));
   pixel[15] = DisplayController.createRawPixel(RGB888(91,62,148));
   pixel[16] = DisplayController.createRawPixel(RGB888(0,0,0));
   pixel[17] = DisplayController.createRawPixel(RGB888(224,0,69));
   pixel[18] = DisplayController.createRawPixel(RGB888(162,62,148));
   pixel[19] = DisplayController.createRawPixel(RGB888(224,62,69));
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
0,0,0,0,0,3,3,3,3,3,3,3,0,0,0,0,0,0,0,0,0,0,0,0,0,0,0,0,0,0,0,0,0,
0,0,0,0,0,0,0,0,0,0,0,0,0,0,0,0,0,0,0,2,2,2,2,2,2,2,2,0,0,0,0,0,0,
0,0,3,3,3,3,3,3,3,3,0,0,0,0,0,0,0,0,0,0,0,0,0,0,0,0,2,0,3,0,0,0,0,
0,2,0,3,0,0,0,0,0,2,0,3,0,0,0,0,0,0,0,3,0,0,0,0,0,2,2,1,0,0,0,0,0,
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
